peakhunt/chinese-diesel-heater-atmega328p/app_common.h

#ifndef __APP_COMMON_DEF_H__
#define __APP_COMMON_DEF_H__

#include <stdint.h>
#include <stdio.h>

#define bool      uint8_t
#define true      1
#define false     0

////////////////////////////////////////////////////////////////////////////////
//
// misc utilities
//
////////////////////////////////////////////////////////////////////////////////

#endif //!__APP_COMMON_DEF_H__
